Baule8520/Einwurfsystem-Arduino/Schrittmotor_1.0_Test/Schrittmotor_1.0_Test.ino

/*
  
  Schrittmotor Test - Hardware: https://www.reichelt.de/arduino-motorsteuerung-inkl-schrittmotor-uln2003a-ard-step-motor-p255289.html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

  By Paul Zech

  Basierend auf dem Stepper Beispiel "stepper_oneRevolution"

 */


#include <Stepper.h>                                // Schrittmotor Library einbinden --> https://www.arduino.cc/en/Reference/Stepper

Stepper Motor(1024, A5, A3, A4, A2);                // Namen des Motors festlegen (Schritte pro Umdrehung festlegen, Anschlusspins (1 bis 4) festlegen)


void setup() {
 
  Motor.setSpeed(1);}                               // Geschwindigkeit festlegen


void loop() {

  Motor.step(1024);                                 // Eine Umdrehung im Uhrzeigersinn
  delay(1000);

  Motor.step(-1024);                                // Eine Umdrehung gegen den Uhrzeigersinn
  delay(1000);}
